ingmarsretro/ESP32_VideoPong/ESP32_VideoPong_V1.0/avatar.h

namespace avatar 
{
const unsigned int xres = 280;
const unsigned int yres = 280;
const unsigned char pixels[] = {
252, 252, 252, 252, 252, 252, 252, 252, 252, 252, 252, 252, 252, 252, 252, 252, 
252, 252, 252, 252, 252, 252, 252, 252, 252, 252, 252, 252, 252, 252, 252, 252, 
252, 252, 251, 251, 252, 252, 252, 252, 252, 252, 252, 252, 252, 252, 252, 252, 
251, 251, 251, 251, 252, 252, 252, 252, 253, 252, 252, 252, 251, 252, 252, 252, 
252, 252, 252, 252, 252, 252, 252, 252, 252, 252, 251, 251, 251, 251, 252, 252, 
252, 252, 252, 252, 252, 252, 252, 252, 252, 252, 252, 252, 252, 252, 252, 252, 
252, 252, 252, 251, 251, 251, 252, 252, 253, 252, 252, 252, 252, 252, 252, 252, 
252, 252, 252, 252, 252, 252, 252, 252, 252, 252, 252, 252, 252, 252, 252, 252, 
252, 252, 252, 252, 252, 252, 252, 252, 252, 252, 252, 252, 252, 252, 252, 252, 
251, 251, 251, 252, 252, 252, 252, 252, 252, 252, 252, 252, 252, 252, 252, 252, 
252, 252, 252, 252, 252, 252, 252, 252, 252, 252, 252, 252, 252, 252, 252, 252, 
252, 252, 252, 252, 252, 252, 252, 252, 251, 251, 251, 252, 252, 252, 251, 251, 
253, 252, 252, 252, 252, 252, 252, 252, 251, 252, 252, 252, 252, 252, 252, 252, 
252, 252, 251, 251, 251, 251, 252, 252, 252, 252, 252, 252, 251, 251, 251, 251, 
252, 252, 253, 252, 252, 252, 252, 252, 252, 252, 252, 252, 252, 252, 252, 252, 
252, 252, 252, 252, 252, 252, 252, 252, 252, 252, 252, 252, 252, 252, 252, 252, 
252, 252, 252, 252, 252, 252, 252, 252, 252, 252, 252, 252, 252, 252, 252, 252, 
252, 252, 252, 252, 252, 252, 252, 252, 253, 253, 253, 253, 253, 253, 253, 253, 
253, 253, 253, 253, 253, 253, 253, 253, 253, 253, 253, 253, 253, 253, 253, 253, 
253, 253, 253, 253, 253, 253, 253, 253, 253, 253, 252, 252, 253, 253, 253, 253, 
253, 253, 253, 253, 253, 253, 253, 253, 252, 252, 253, 253, 253, 253, 253, 253, 
253, 253, 253, 252, 252, 253, 253, 253, 253, 253, 253, 253, 253, 253, 253, 253, 
253, 253, 252, 252, 252, 252, 253, 253, 252, 252, 253, 253, 253, 253, 253, 253, 
253, 253, 253, 253, 253, 253, 253, 253, 252, 252, 252, 252, 252, 252, 253, 253, 
253, 253, 253, 253, 253, 253, 253, 253, 253, 253, 253, 253, 253, 253, 253, 253, 
253, 252, 252, 252, 252, 253, 253, 253, 253, 253, 253, 253, 253, 253, 253, 253, 
253, 253, 253, 253, 253, 253, 253, 253, 252, 252, 252, 252, 252, 253, 253, 253, 
253, 253, 253, 253, 253, 253, 253, 253, 252, 252, 253, 253, 253, 253, 252, 252, 
253, 253, 253, 253, 253, 253, 253, 253, 253, 253, 253, 253, 253, 253, 253, 253, 
253, 253, 253, 253, 253, 253, 253, 253, 253, 253, 253, 253, 253, 253, 253, 252, 
252, 253, 253, 253, 253, 253, 253, 253, 253, 253, 252, 252, 252, 252, 253, 253, 
253, 253, 253, 253, 253, 253, 253, 253, 252, 253, 253, 253, 252, 252, 253, 253, 
253, 253, 253, 253, 253, 253, 253, 253, 253, 253, 253, 253, 253, 253, 253, 253, 
253, 253, 253, 253, 253, 253, 253, 253, 253, 253, 253, 253, 253, 253, 253, 253, 
253, 253, 253, 253, 253, 253, 253, 253, 253, 253, 253, 253, 253, 253, 253, 253, 
253, 253, 253, 253, 253, 253, 253, 253, 253, 253, 253, 253, 253, 253, 253, 253, 
253, 253, 253, 253, 253, 253, 253, 253, 253, 253, 253, 253, 253, 253, 253, 253, 
254, 253, 253, 253, 253, 254, 254, 253, 253, 253, 253, 253, 253, 253, 253, 253, 
253, 253, 253, 253, 253, 253, 253, 253, 253, 253, 253, 253, 253, 253, 253, 254, 
253, 253, 253, 253, 253, 253, 253, 253, 253, 253, 253, 253, 253, 253, 253, 253, 
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
};
